rockola/stomp-breakout/images/bottom.png

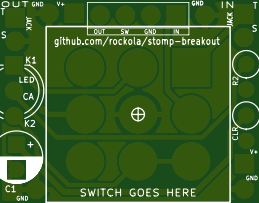
images/bottom.png
