rockola/stomp-breakout/images/stomp-breakout-B_Cu.gbl.png

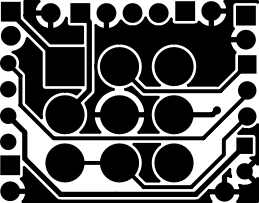
images/stomp-breakout-B_Cu.gbl.png
