rockola/stomp-breakout/images/stomp-breakout-B_SilkS.gbo.png

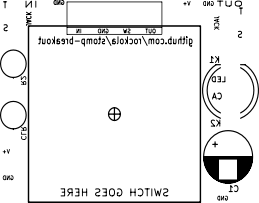
images/stomp-breakout-B_SilkS.gbo.png
