rockola/stomp-breakout/images/stomp-breakout-F_Cu.gtl.png

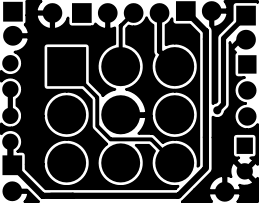
images/stomp-breakout-F_Cu.gtl.png
