rockola/stomp-breakout/images/stomp-breakout-oshpark-back.png

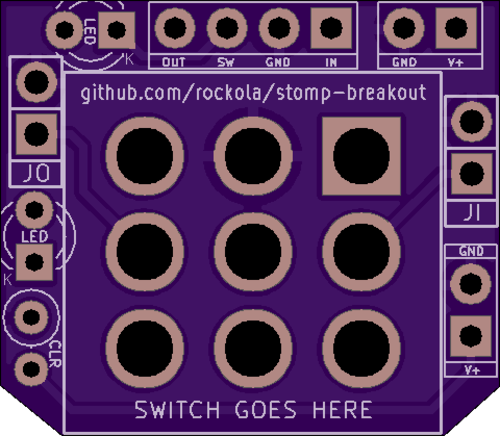
images/stomp-breakout-oshpark-back.png
