rockola/stomp-breakout/images/stomp-breakout-oshpark-front.png

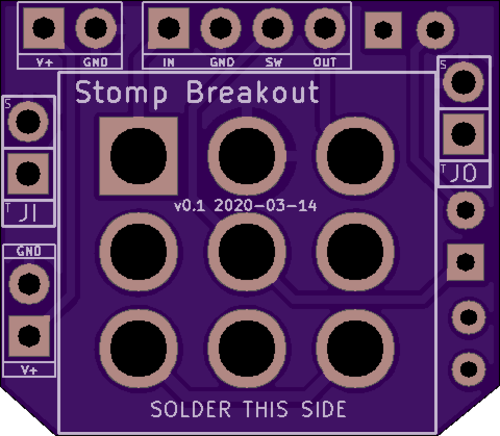
images/stomp-breakout-oshpark-front.png
