rockola/stomp-breakout/images/v0.4_top.png

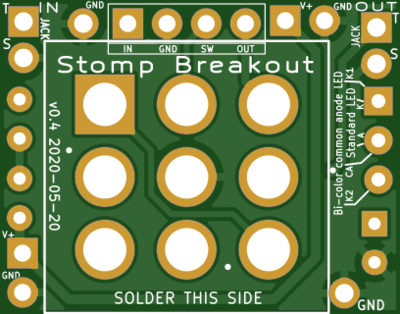
images/v0.4_top.png
